blablabananarama/sage/docs/img/intent/corner-options.jpg

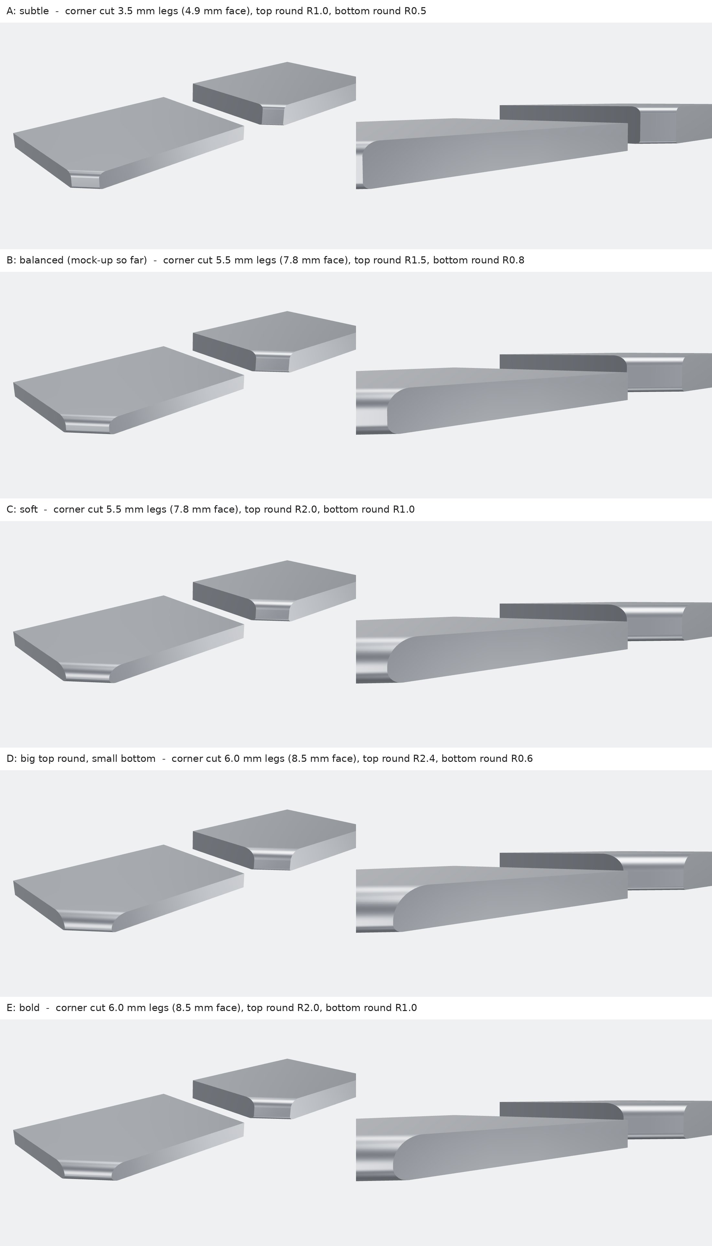
docs/img/intent/corner-options.jpg
