blablabananarama/sage/docs/img/intent/plan.png

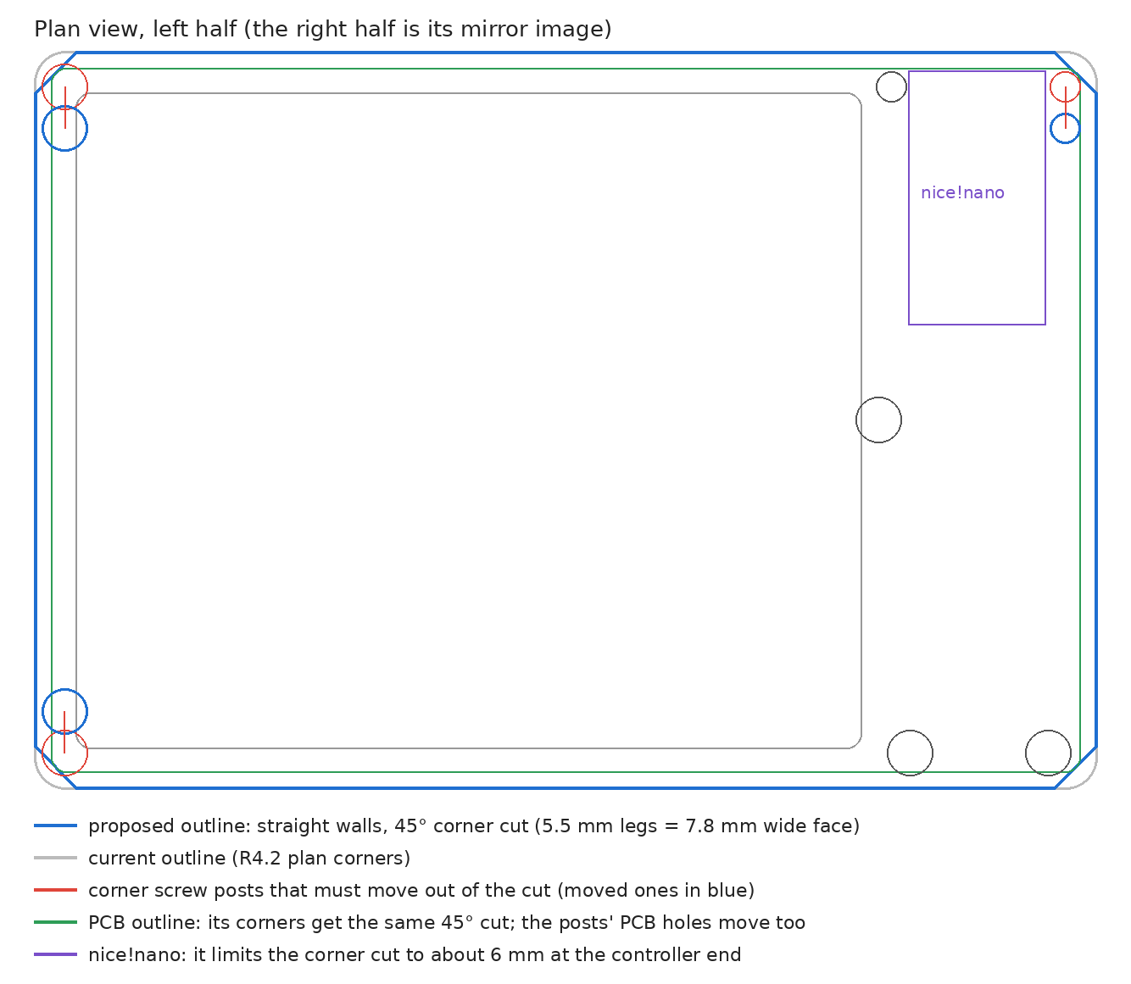
docs/img/intent/plan.png
